TreshanAyesh/Analog-Function-Generator/ProductTestings/IMG_20220408_100124.jpg

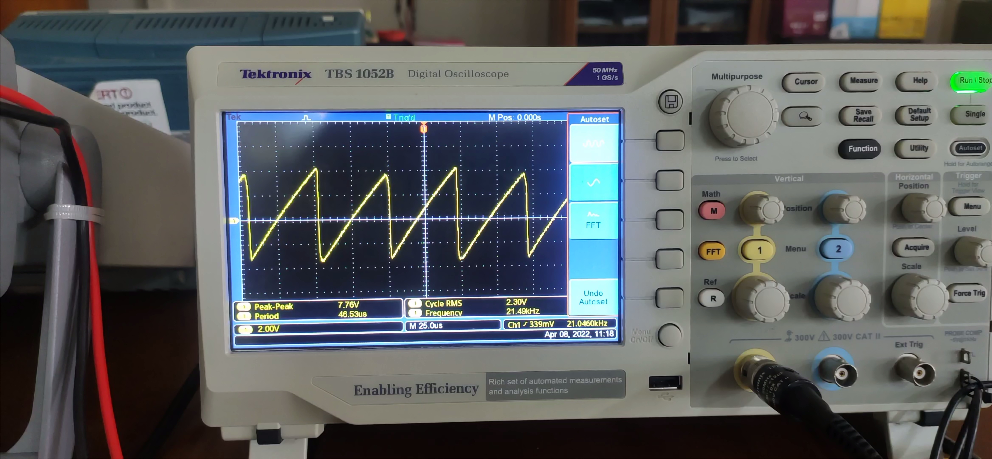
ProductTestings/IMG_20220408_100124.jpg
